delhatch/PiPod_ePaper/Pictures/back2.jpg

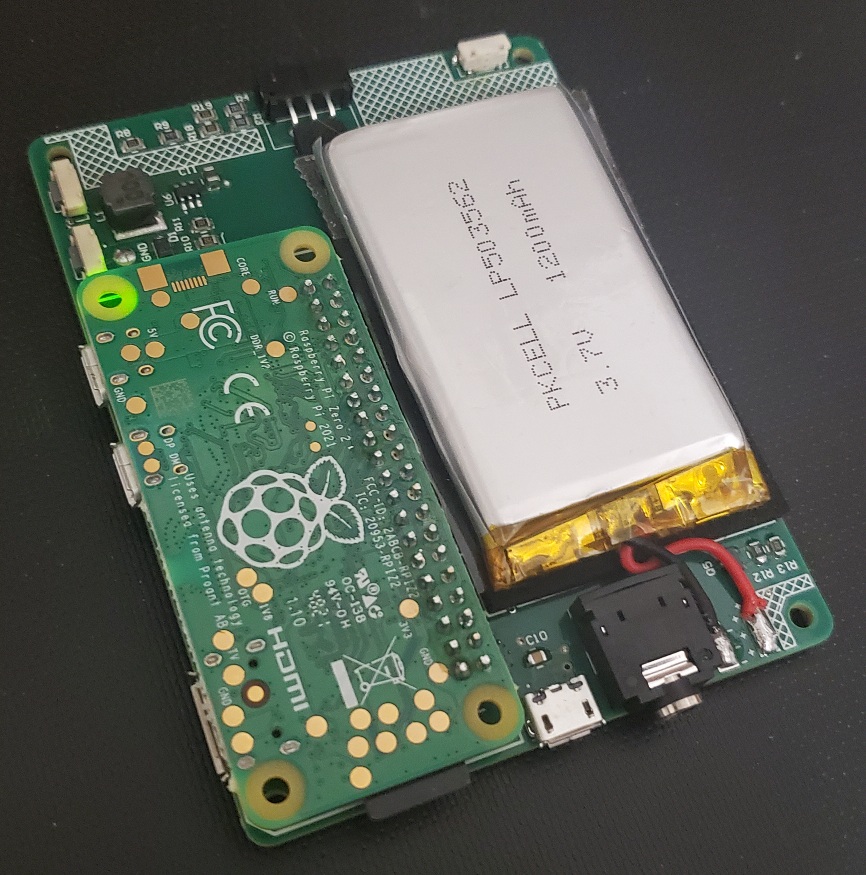
Pictures/back2.jpg
