delhatch/PiPod_ePaper/Pictures/bot_w_batt_v2.jpg

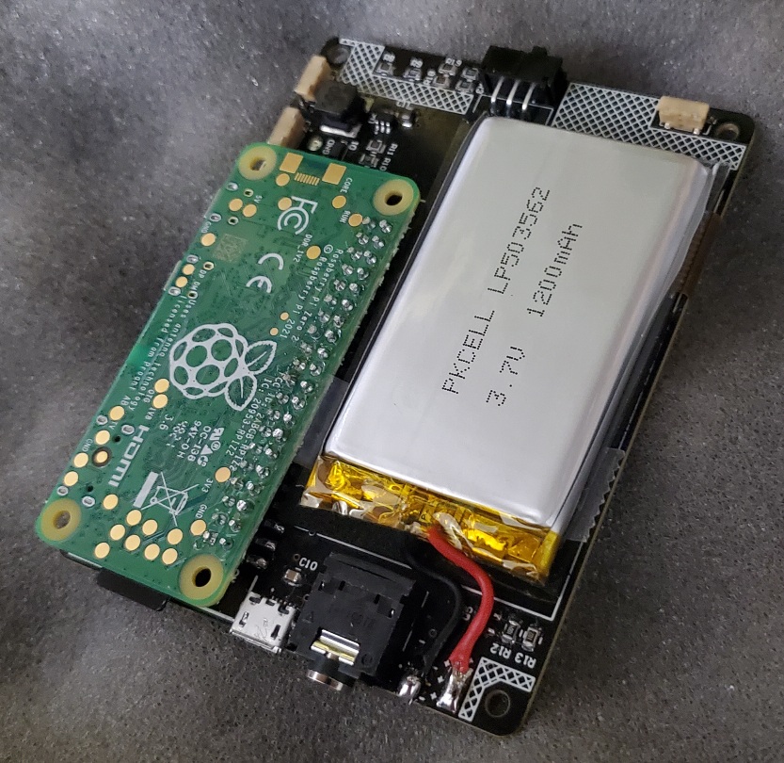
Pictures/bot_w_batt_v2.jpg
