delhatch/PiPod_ePaper/Pictures/front_led.jpg

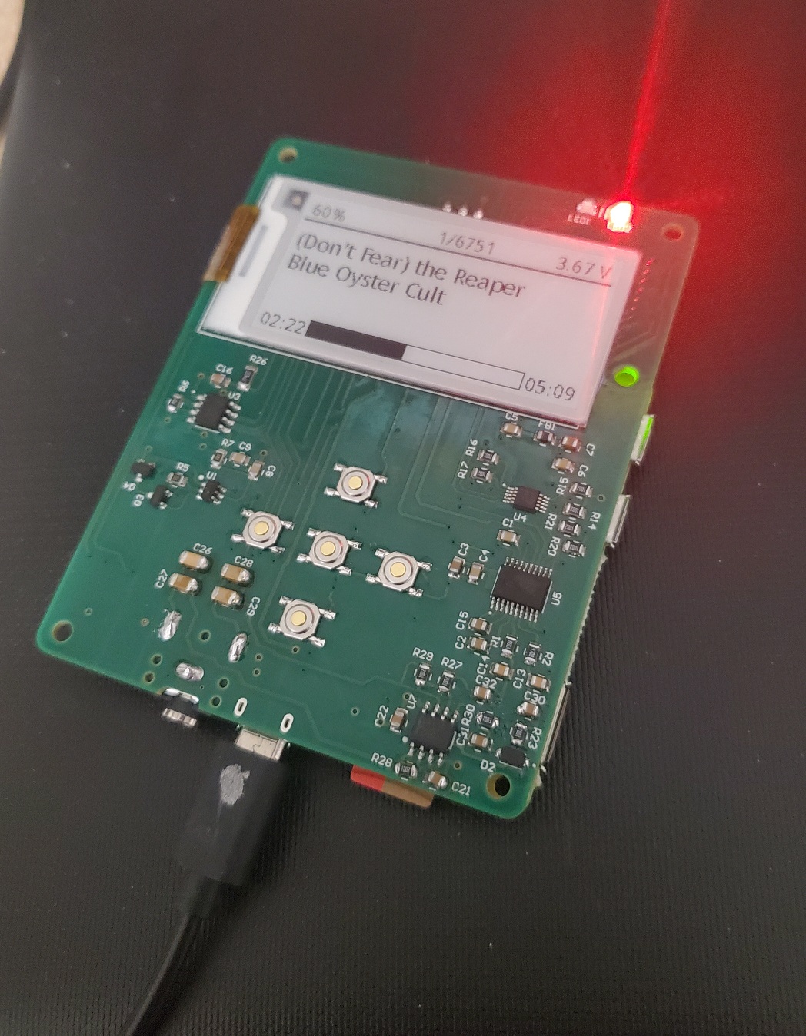
Pictures/front_led.jpg
