delhatch/PiPod_ePaper/Pictures/front_playing.jpg

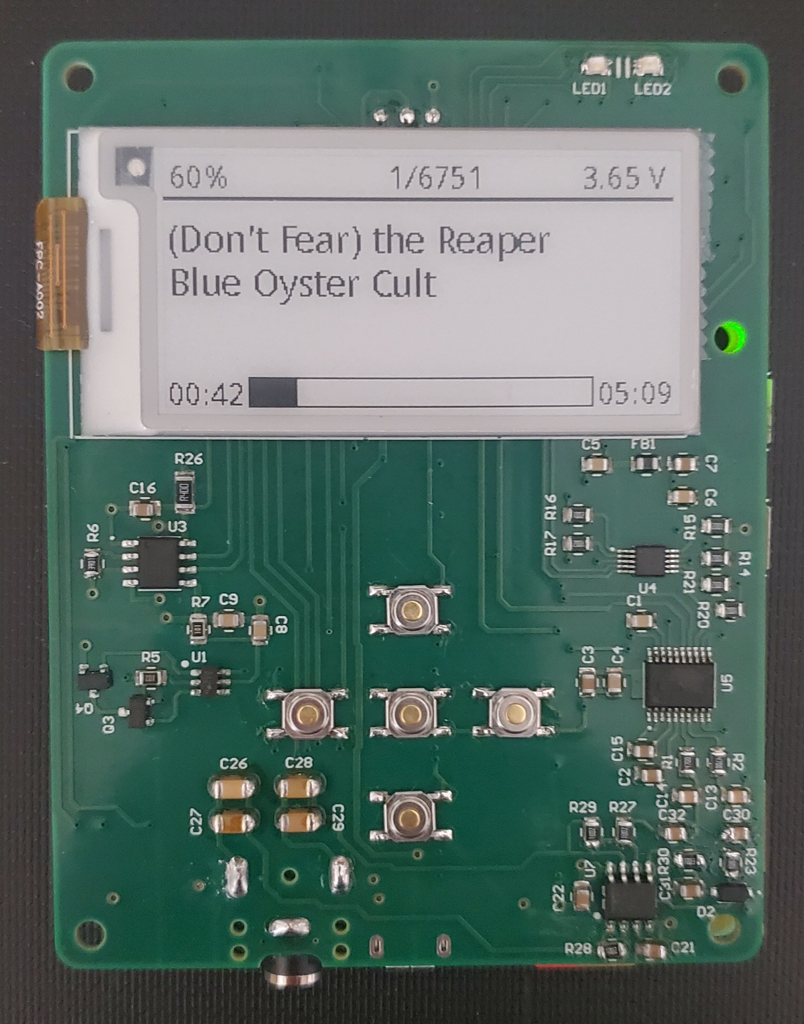
Pictures/front_playing.jpg
