delhatch/PiPod_ePaper/Pictures/PCB_top.JPG

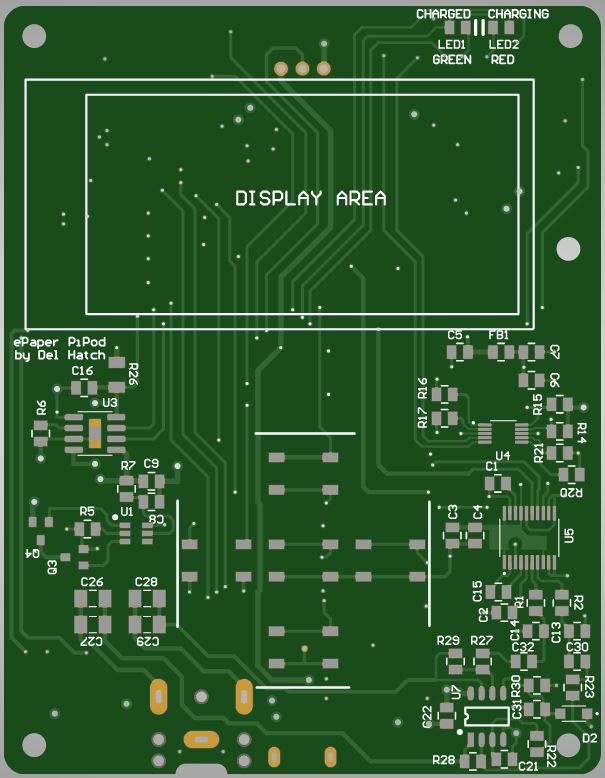
Pictures/PCB_top.JPG
