delhatch/PiPod_ePaper/Pictures/PCB_parts_bottom.JPG

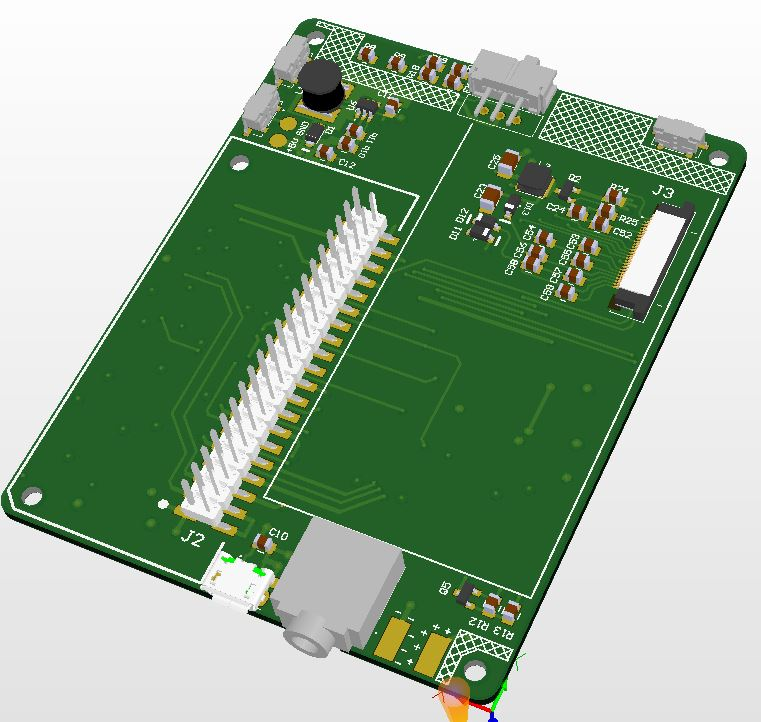
Pictures/PCB_parts_bottom.JPG
